lbrmnk/arduino-emoncms-client/dallastempsensor.cpp

#include "dallastempsensor.h"
#include "utils.h"

DallasTempSensor::DallasTempSensor(DallasTemperature* sensors, DeviceAddress addr) 
{
  _sensors = sensors;
  _temp = 0;

  memcpy(_address, addr, sizeof(DeviceAddress));
  sensors->setResolution(addr, 12);
}

DallasTempSensor*
DallasTempSensor::createByIndex(DallasTemperature* sensors, byte index)
{
  DeviceAddress addr;      
  sensors->getAddress(addr, index);
  return new DallasTempSensor(sensors, addr);
}

char* 
DallasTempSensor::addressToString(DeviceAddress addr) {
  return addressToString(__id_buffer, addr);
}

char* 
DallasTempSensor::addressToString(char * buf, DeviceAddress addr) {
  Utils::bytesToString(buf, addr, 8);
  return buf;
}

bool 
DallasTempSensor::measure() 
{
  // _sensors->requestTemperaturesByIndex(_index);
  if (_sensors->requestTemperaturesByAddress(_address)) {
    int raw = _sensors->getTemp(_address);
    if (raw != DEVICE_DISCONNECTED_RAW && raw != 0x2A80 /* 85 C error */) {
      _temp = DallasTemperature::rawToCelsius(raw);
      return true;
    }
  }
  return false;
}

float 
DallasTempSensor::getValue() 
{ 
  return _temp;
}

char *
DallasTempSensor::getId() 
{
  return addressToString(_address);
}
